McOrts/hand_tool_anemometer/docs/images/HTA_Arlarm.jpg

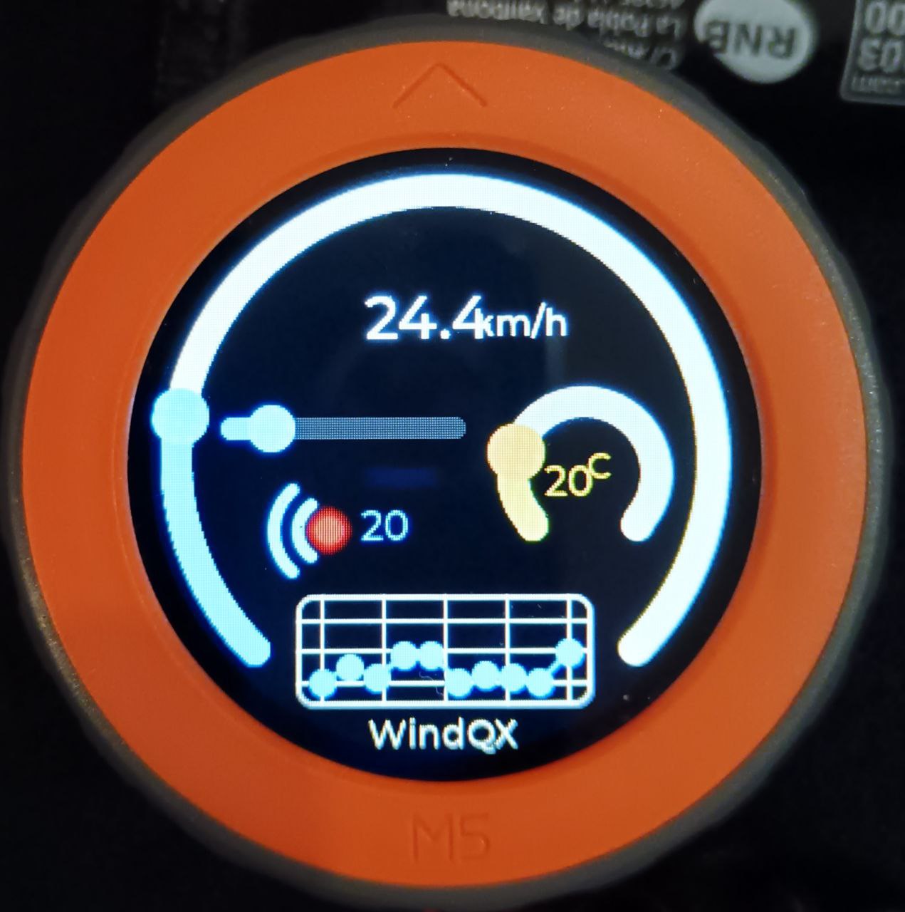
docs/images/HTA_Arlarm.jpg
