McOrts/hand_tool_anemometer/docs/images/HTA_end.jpg

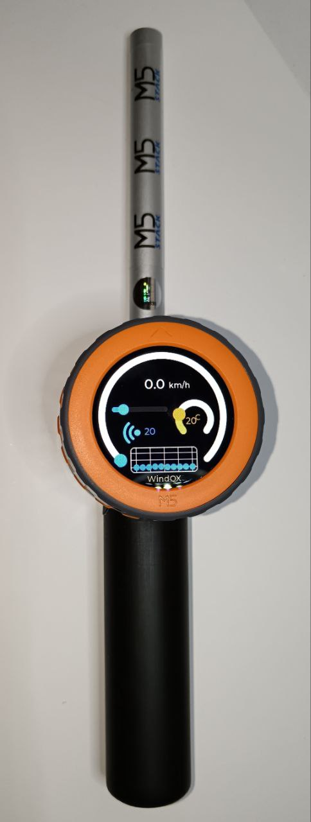
docs/images/HTA_end.jpg
