McOrts/hand_tool_anemometer/docs/images/M5D_pinOut.png

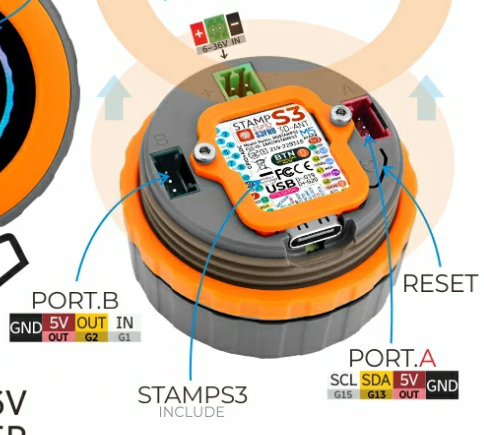
docs/images/M5D_pinOut.png
